laserblade41/FinProj/pics/backside.png

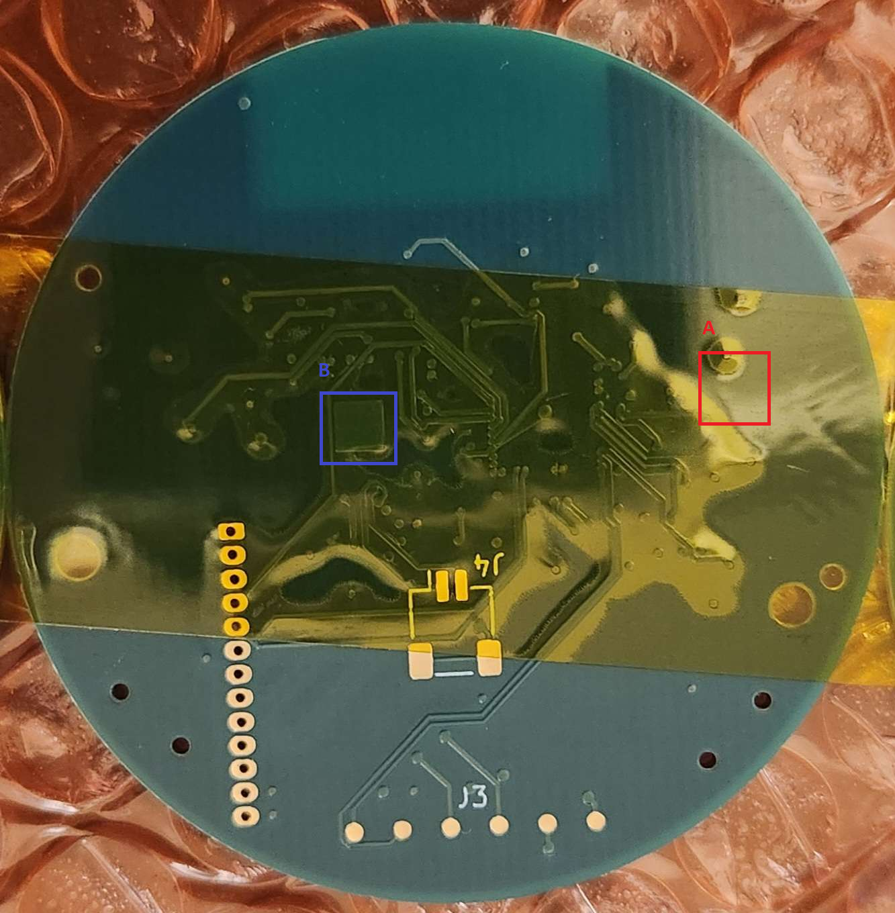
pics/backside.png
