laserblade41/FinProj/pics/components.jpg

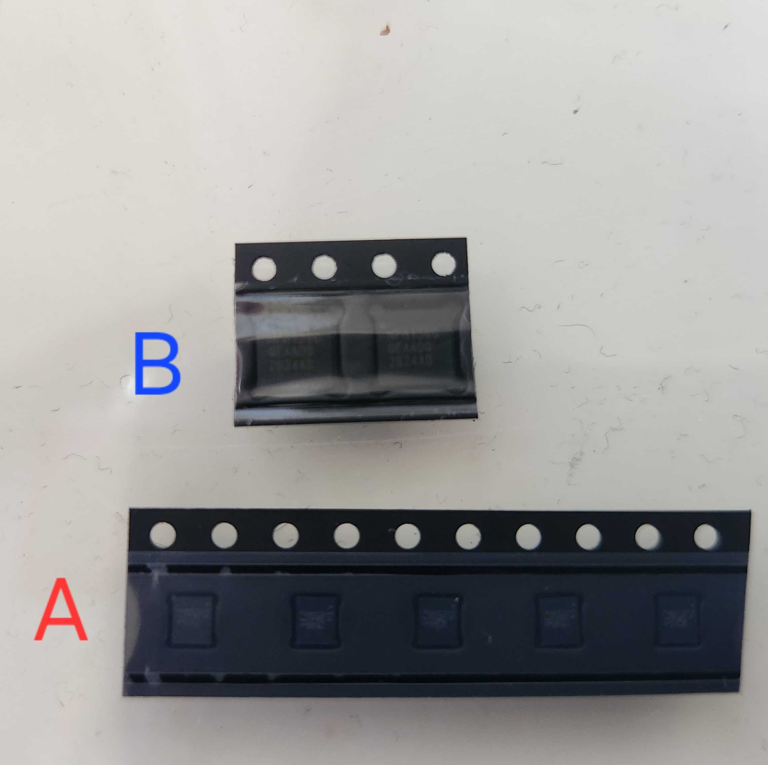
pics/components.jpg
